edger477/FOC-Stim/case/20241209_165336.jpg

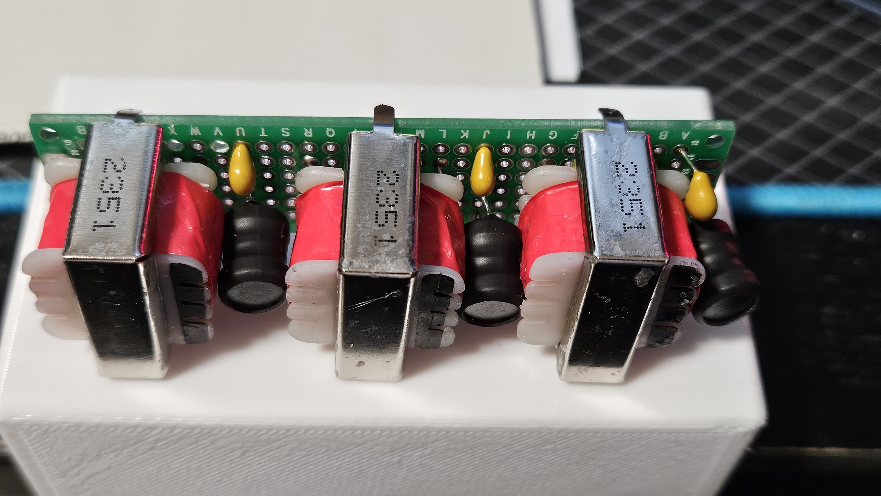
case/20241209_165336.jpg
