edger477/FOC-Stim/case/20241209_165359.jpg

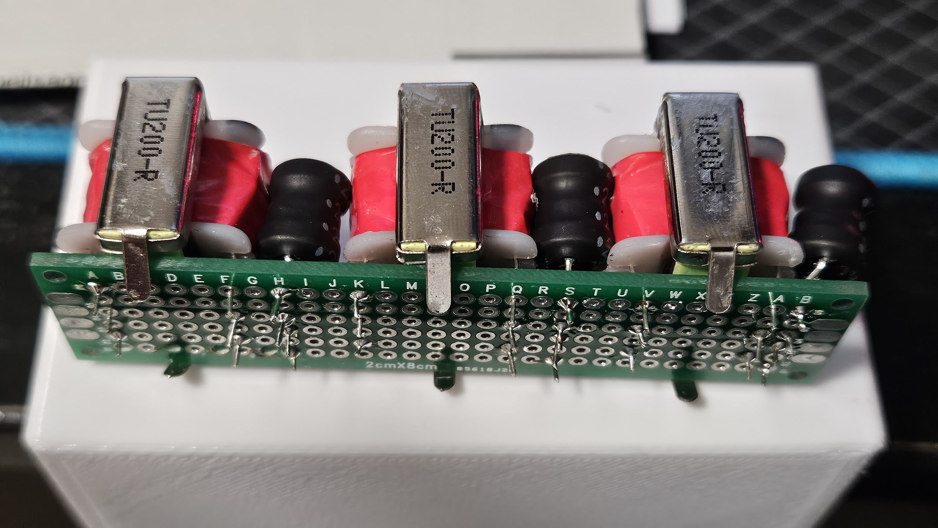
case/20241209_165359.jpg
