edger477/FOC-Stim/case/20241209_170253.jpg

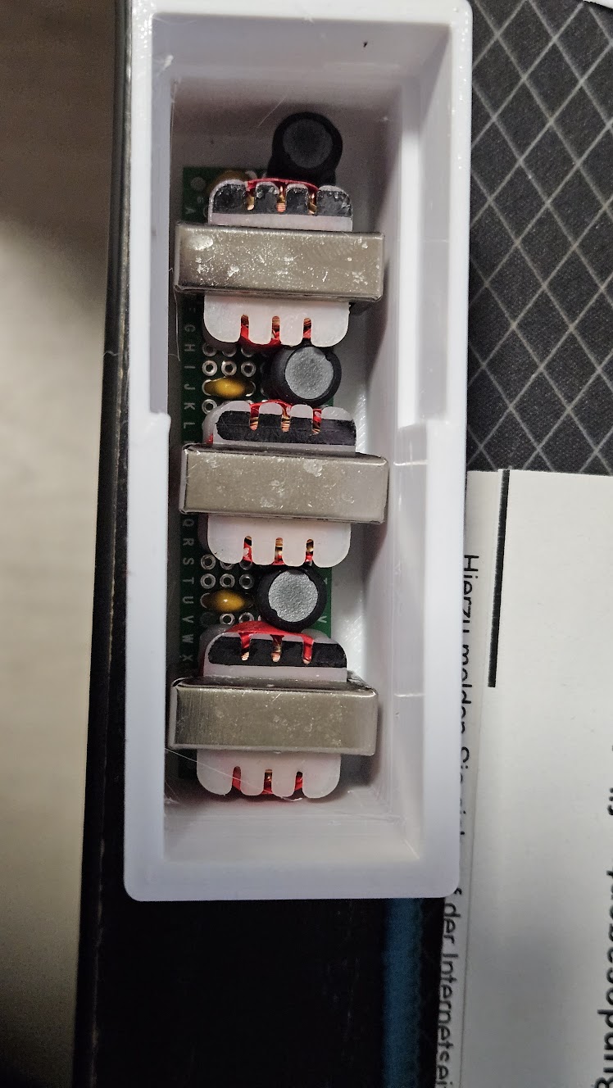
case/20241209_170253.jpg
