edger477/FOC-Stim/case/20241209_173533.jpg

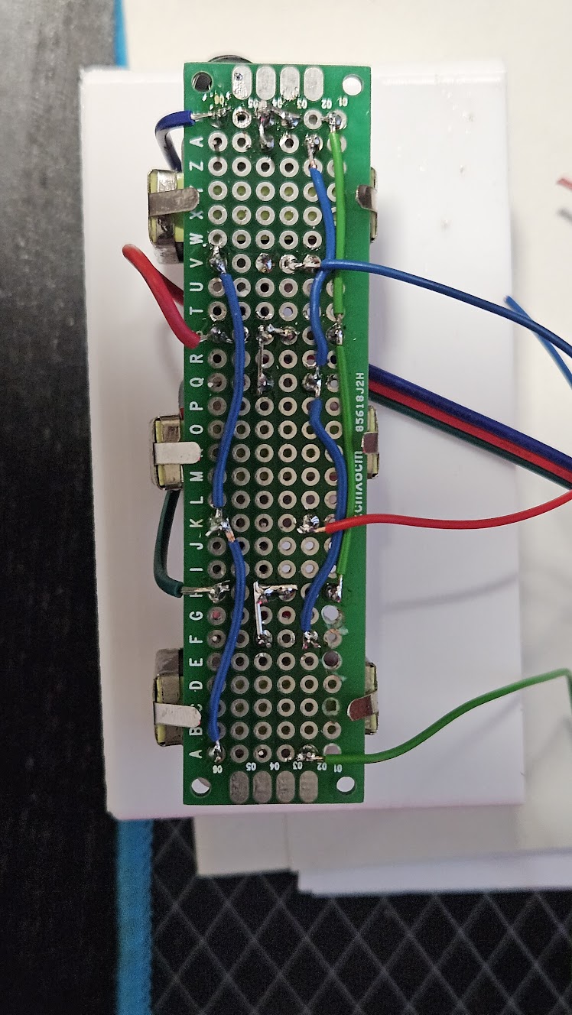
case/20241209_173533.jpg
