edger477/FOC-Stim/case/20241210_161650.jpg

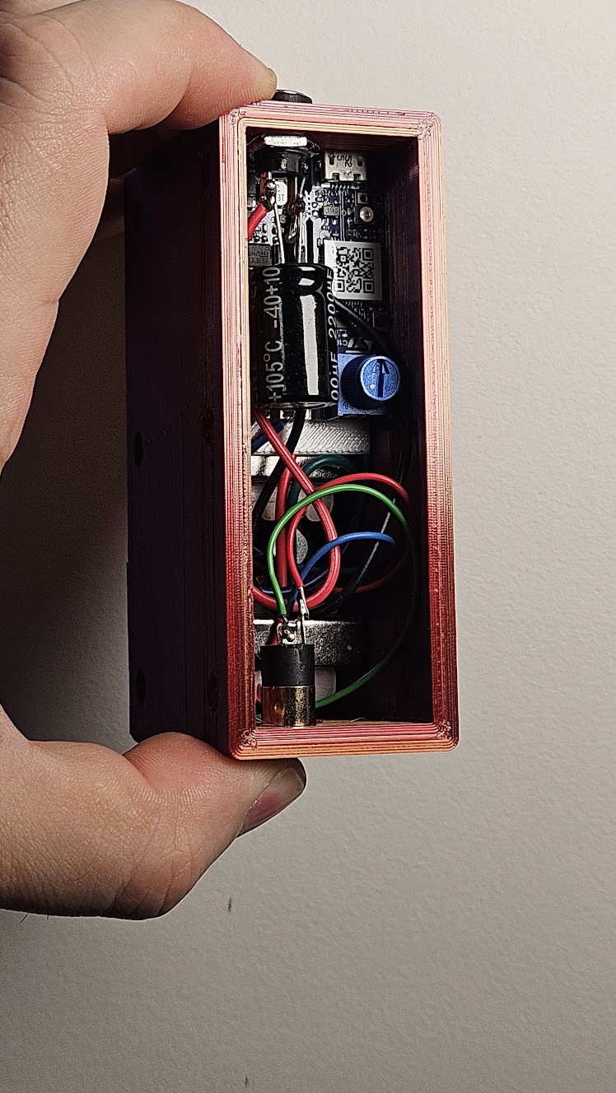
case/20241210_161650.jpg
